WayneGretzky1/EE-3951W/strained_gauge/ADC_example/bye00035_adc_v001.h

/* 
 * File:   bye00035_adc_v001.h
 * Author: bye00035
 *
 * Created on April 7, 2023, 11:47 AM
 */

#ifndef BYE00035_ADC_V001_H
#define	BYE00035_ADC_V001_H

#ifdef	__cplusplus
extern "C" {
#endif
    void adc_init();
    void timer1_init();
#ifdef	__cplusplus
}
#endif

#endif	/* BYE00035_ADC_V001_H */
