WayneGretzky1/EE-3951W/strained_gauge/ADC_example/bye00035_circularBuffer_v001.h

/* 
 * File:   bye00035_circularBuffer_v001.h
 * Author: bye00035
 *
 * Created on April 7, 2023, 11:23 AM
 */

#ifndef BYE00035_CIRCULARBUFFER_V001_H
#define	BYE00035_CIRCULARBUFFER_V001_H

#ifdef	__cplusplus
extern "C" {
#endif
    void initBuffer();
    void putVal(int ADCvalue);
    unsigned int getAvg();
#ifdef	__cplusplus
}
#endif

#endif	/* BYE00035_CIRCULARBUFFER_V001_H */
